DL1XY/YM2149_ESP32/main/rest_common.c

/*
 * rest_common.c
 *
 *  Created on: 17.03.2020
 *      Author: arnew
 */


#include "rest_common.h"

static const char *REST_TAG = "esp-rest";


/* Set HTTP response content type according to file extension */
esp_err_t set_content_type_from_file(httpd_req_t *req, const char *filepath)
{
    const char *type = "text/plain";
    if (CHECK_FILE_EXTENSION(filepath, ".html")) {
        type = "text/html";
    } else if (CHECK_FILE_EXTENSION(filepath, ".js")) {
        type = "application/javascript";
    } else if (CHECK_FILE_EXTENSION(filepath, ".css")) {
        type = "text/css";
    } else if (CHECK_FILE_EXTENSION(filepath, ".png")) {
        type = "image/png";
    } else if (CHECK_FILE_EXTENSION(filepath, ".ico")) {
        type = "image/x-icon";
    } else if (CHECK_FILE_EXTENSION(filepath, ".svg")) {
        type = "text/xml";
    }
    return httpd_resp_set_type(req, type);
}

esp_err_t rest_common_get_handler(httpd_req_t *req)
{
    char filepath[FILE_PATH_MAX];

    rest_server_context_t *rest_context = (rest_server_context_t *)req->user_ctx;
    strlcpy(filepath, rest_context->base_path, sizeof(filepath));
    if (req->uri[strlen(req->uri) - 1] == '/') {
        strlcat(filepath, "/index.html", sizeof(filepath));
    } else {
        strlcat(filepath, req->uri, sizeof(filepath));
    }
    int fd = open(filepath, O_RDONLY, 0);
    if (fd == -1) {
        ESP_LOGE(REST_TAG, "Failed to open file : %s", filepath);
        /* Respond with 500 Internal Server Error */
        httpd_resp_send_err(req, HTTPD_500_INTERNAL_SERVER_ERROR, "Failed to read existing file");
        return ESP_FAIL;
    }

    set_content_type_from_file(req, filepath);

    char *chunk = rest_context->scratch;
    ssize_t read_bytes;
    do {
        /* Read file in chunks into the scratch buffer */
        read_bytes = read(fd, chunk, SCRATCH_BUFSIZE);
        if (read_bytes == -1) {
            ESP_LOGE(REST_TAG, "Failed to read file : %s", filepath);
        } else if (read_bytes > 0) {
            /* Send the buffer contents as HTTP response chunk */
            if (httpd_resp_send_chunk(req, chunk, read_bytes) != ESP_OK) {
                close(fd);
                ESP_LOGE(REST_TAG, "File sending failed!");
                /* Abort sending file */
                httpd_resp_sendstr_chunk(req, NULL);
                /* Respond with 500 Internal Server Error */
                httpd_resp_send_err(req, HTTPD_500_INTERNAL_SERVER_ERROR, "Failed to send file");
                return ESP_FAIL;
            }
        }
    } while (read_bytes > 0);
    /* Close file after sending complete */
    close(fd);
    ESP_LOGI(REST_TAG, "File sending complete");
    /* Respond with an empty chunk to signal HTTP response completion */
    httpd_resp_send_chunk(req, NULL, 0);
    return ESP_OK;
}
