DL1XY/YM2149_ESP32/main/secrets_example.h

/*
 * secrets.h
 *
 *  Created on: 28.04.2020
 *      Author: DL1XY
 */

#ifndef MAIN_SECRETS_H_
#define MAIN_SECRETS_H_

#define ESP_WIFI_SSID "YOUR_SSID"
#define ESP_WIFI_PASS "YOUR_PASSWORD"
#define MAX_STA_CONN 1 // No one else should be connected

#endif /* MAIN_SECRETS_H_ */
